NomiChirps/tplp2/tplp/hx8357/lvgl_driver.h

#ifndef TPLP_HX8357_LVGL_DRIVER_H_
#define TPLP_HX8357_LVGL_DRIVER_H_

#include "lvgl/lvgl.h"
#include "tplp/hx8357/hx8357.h"

namespace tplp {

// This driver makes use of the 0th task notification index on the
// lv_timer_handler task.
lv_disp_t* RegisterDisplayDriver_HX8357(int priority, int stack_depth,
                                        HX8357* display,
                                        TaskHandle_t lv_timer_task);

}  // namespace tplp

#endif  // TPLP_HX8357_LVGL_DRIVER_H_
