NomiChirps/tplp2/tplp/tsc2007/tsc2007_lvgl_driver.h

#ifndef TPLP_TSC2007_TSC2007_LVGL_DRIVER_H_
#define TPLP_TSC2007_TSC2007_LVGL_DRIVER_H_

#include "lvgl/lvgl.h"
#include "tplp/tsc2007/tsc2007.h"

namespace tplp {

lv_indev_t* RegisterInputDevice_TSC2007(TSC2007* touchscreen);

}  // namespace tplp

#endif  // TPLP_TSC2007_TSC2007_LVGL_DRIVER_H_
