NomiChirps/tplp2/absl/strings/charconv.cc

// Copyright 2018 The Abseil Authors.
//
// Licensed under the Apache License, Version 2.0 (the "License");
// you may not use this file except in compliance with the License.
// You may obtain a copy of the License at
//
//      https://www.apache.org/licenses/LICENSE-2.0
//
// Unless required by applicable law or agreed to in writing, software
// distributed under the License is distributed on an "AS IS" BASIS,
// WITHOUT WARRANTIES OR CONDITIONS OF ANY KIND, either express or implied.
// See the License for the specific language governing permissions and
// limitations under the License.

#include "absl/strings/charconv.h"

#include <algorithm>
#include <cassert>
#include <cmath>
#include <cstring>
#include <limits>

#include "absl/base/casts.h"
#include "absl/numeric/bits.h"
#include "absl/numeric/int128.h"
#include "absl/strings/internal/charconv_bigint.h"
#include "absl/strings/internal/charconv_parse.h"

// The macro ABSL_BIT_PACK_FLOATS is defined on x86-64, where IEEE floating
// point numbers have the same endianness in memory as a bitfield struct
// containing the corresponding parts.
//
// When set, we replace calls to ldexp() with manual bit packing, which is
// faster and is unaffected by floating point environment.
#ifdef ABSL_BIT_PACK_FLOATS
#error ABSL_BIT_PACK_FLOATS cannot be directly set
#elif defined(__x86_64__) || defined(_M_X64)
#define ABSL_BIT_PACK_FLOATS 1
#endif

// A note about subnormals:
//
// The code below talks about "normals" and "subnormals".  A normal IEEE float
// has a fixed-width mantissa and power of two exponent.  For example, a normal
// `double` has a 53-bit mantissa.  Because the high bit is always 1, it is not
// stored in the representation.  The implicit bit buys an extra bit of
// resolution in the datatype.
//
// The downside of this scheme is that there is a large gap between DBL_MIN and
// zero.  (Large, at least, relative to the different between DBL_MIN and the
// next representable number).  This gap is softened by the "subnormal" numbers,
// which have the same power-of-two exponent as DBL_MIN, but no implicit 53rd
// bit.  An all-bits-zero exponent in the encoding represents subnormals.  (Zero
// is represented as a subnormal with an all-bits-zero mantissa.)
//
// The code below, in calculations, represents the mantissa as a uint64_t.  The
// end result normally has the 53rd bit set.  It represents subnormals by using
// narrower mantissas.

namespace absl {
ABSL_NAMESPACE_BEGIN
namespace {

template <typename FloatType>
struct FloatTraits;

template <>
struct FloatTraits<double> {
  using mantissa_t = uint64_t;

  // The number of mantissa bits in the given float type.  This includes the
  // implied high bit.
  static constexpr int kTargetMantissaBits = 53;

  // The largest supported IEEE exponent, in our integral mantissa
  // representation.
  //
  // If `m` is the largest possible int kTargetMantissaBits bits wide, then
  // m * 2**kMaxExponent is exactly equal to DBL_MAX.
  static constexpr int kMaxExponent = 971;

  // The smallest supported IEEE normal exponent, in our integral mantissa
  // representation.
  //
  // If `m` is the smallest possible int kTargetMantissaBits bits wide, then
  // m * 2**kMinNormalExponent is exactly equal to DBL_MIN.
  static constexpr int kMinNormalExponent = -1074;

  static double MakeNan(const char* tagp) {
    // Support nan no matter which namespace it's in.  Some platforms
    // incorrectly don't put it in namespace std.
    using namespace std;  // NOLINT
    return nan(tagp);
  }

  // Builds a nonzero floating point number out of the provided parts.
  //
  // This is intended to do the same operation as ldexp(mantissa, exponent),
  // but using purely integer math, to avoid -ffastmath and floating
  // point environment issues.  Using type punning is also faster. We fall back
  // to ldexp on a per-platform basis for portability.
  //
  // `exponent` must be between kMinNormalExponent and kMaxExponent.
  //
  // `mantissa` must either be exactly kTargetMantissaBits wide, in which case
  // a normal value is made, or it must be less narrow than that, in which case
  // `exponent` must be exactly kMinNormalExponent, and a subnormal value is
  // made.
  static double Make(mantissa_t mantissa, int exponent, bool sign) {
#ifndef ABSL_BIT_PACK_FLOATS
    // Support ldexp no matter which namespace it's in.  Some platforms
    // incorrectly don't put it in namespace std.
    using namespace std;  // NOLINT
    return sign ? -ldexp(mantissa, exponent) : ldexp(mantissa, exponent);
#else
    constexpr uint64_t kMantissaMask =
        (uint64_t{1} << (kTargetMantissaBits - 1)) - 1;
    uint64_t dbl = static_cast<uint64_t>(sign) << 63;
    if (mantissa > kMantissaMask) {
      // Normal value.
      // Adjust by 1023 for the exponent representation bias, and an additional
      // 52 due to the implied decimal point in the IEEE mantissa
      // representation.
      dbl += static_cast<uint64_t>(exponent + 1023 + kTargetMantissaBits - 1)
             << 52;
      mantissa &= kMantissaMask;
    } else {
      // subnormal value
      assert(exponent == kMinNormalExponent);
    }
    dbl += mantissa;
    return absl::bit_cast<double>(dbl);
#endif  // ABSL_BIT_PACK_FLOATS
  }
};

// Specialization of floating point traits for the `float` type.  See the
// FloatTraits<double> specialization above for meaning of each of the following
// members and methods.
template <>
struct FloatTraits<float> {
  using mantissa_t = uint32_t;

  static constexpr int kTargetMantissaBits = 24;
  static constexpr int kMaxExponent = 104;
  static constexpr int kMinNormalExponent = -149;

  static float MakeNan(const char* tagp) {
    // Support nanf no matter which namespace it's in.  Some platforms
    // incorrectly don't put it in namespace std.
    using namespace std;  // NOLINT
    return nanf(tagp);
  }

  static float Make(mantissa_t mantissa, int exponent, bool sign) {
#ifndef ABSL_BIT_PACK_FLOATS
    // Support ldexpf no matter which namespace it's in.  Some platforms
    // incorrectly don't put it in namespace std.
    using namespace std;  // NOLINT
    return sign ? -ldexpf(mantissa, exponent) : ldexpf(mantissa, exponent);
#else
    constexpr uint32_t kMantissaMask =
        (uint32_t{1} << (kTargetMantissaBits - 1)) - 1;
    uint32_t flt = static_cast<uint32_t>(sign) << 31;
    if (mantissa > kMantissaMask) {
      // Normal value.
      // Adjust by 127 for the exponent representation bias, and an additional
      // 23 due to the implied decimal point in the IEEE mantissa represenation.
      flt += static_cast<uint32_t>(exponent + 127 + kTargetMantissaBits - 1)
             << 23;
      mantissa &= kMantissaMask;
    } else {
      // subnormal value
      assert(exponent == kMinNormalExponent);
    }
    flt += mantissa;
    return absl::bit_cast<float>(flt);
#endif  // ABSL_BIT_PACK_FLOATS
  }
};

// Decimal-to-binary conversions require coercing powers of 10 into a mantissa
// and a power of 2.  The two helper functions Power10Mantissa(n) and
// Power10Exponent(n) perform this task.  Together, these represent a hand-
// rolled floating point value which is equal to or just less than 10**n.
//
// The return values satisfy two range guarantees:
//
//   Power10Mantissa(n) * 2**Power10Exponent(n) <= 10**n
//     < (Power10Mantissa(n) + 1) * 2**Power10Exponent(n)
//
//   2**63 <= Power10Mantissa(n) < 2**64.
//
// Lookups into the power-of-10 table must first check the Power10Overflow() and
// Power10Underflow() functions, to avoid out-of-bounds table access.
//
// Indexes into these tables are biased by -kPower10TableMin, and the table has
// values in the range [kPower10TableMin, kPower10TableMax].
extern const uint64_t kPower10MantissaHighTable[];  // High 64 of 128 bits.
extern const uint64_t kPower10MantissaLowTable[];   // Low  64 of 128 bits.
extern const int16_t kPower10ExponentTable[];

// The smallest (inclusive) allowed value for use with the Power10Mantissa()
// and Power10Exponent() functions below.  (If a smaller exponent is needed in
// calculations, the end result is guaranteed to underflow.)
constexpr int kPower10TableMin = -342;

// The largest (inclusive) allowed value for use with the Power10Mantissa() and
// Power10Exponent() functions below.  (If a smaller exponent is needed in
// calculations, the end result is guaranteed to overflow.)
constexpr int kPower10TableMax = 308;

uint64_t Power10Mantissa(int n) {
  return kPower10MantissaHighTable[n - kPower10TableMin];
}

int Power10Exponent(int n) {
  return kPower10ExponentTable[n - kPower10TableMin];
}

// Returns true if n is large enough that 10**n always results in an IEEE
// overflow.
bool Power10Overflow(int n) { return n > kPower10TableMax; }

// Returns true if n is small enough that 10**n times a ParsedFloat mantissa
// always results in an IEEE underflow.
bool Power10Underflow(int n) { return n < kPower10TableMin; }

// Returns true if Power10Mantissa(n) * 2**Power10Exponent(n) is exactly equal
// to 10**n numerically.  Put another way, this returns true if there is no
// truncation error in Power10Mantissa(n).
bool Power10Exact(int n) { return n >= 0 && n <= 27; }

// Sentinel exponent values for representing numbers too large or too close to
// zero to represent in a double.
constexpr int kOverflow = 99999;
constexpr int kUnderflow = -99999;

// Struct representing the calculated conversion result of a positive (nonzero)
// floating point number.
//
// The calculated number is mantissa * 2**exponent (mantissa is treated as an
// integer.)  `mantissa` is chosen to be the correct width for the IEEE float
// representation being calculated.  (`mantissa` will always have the same bit
// width for normal values, and narrower bit widths for subnormals.)
//
// If the result of conversion was an underflow or overflow, exponent is set
// to kUnderflow or kOverflow.
struct CalculatedFloat {
  uint64_t mantissa = 0;
  int exponent = 0;
};

// Returns the bit width of the given uint128.  (Equivalently, returns 128
// minus the number of leading zero bits.)
int BitWidth(uint128 value) {
  if (Uint128High64(value) == 0) {
    return bit_width(Uint128Low64(value));
  }
  return 128 - countl_zero(Uint128High64(value));
}

// Calculates how far to the right a mantissa needs to be shifted to create a
// properly adjusted mantissa for an IEEE floating point number.
//
// `mantissa_width` is the bit width of the mantissa to be shifted, and
// `binary_exponent` is the exponent of the number before the shift.
//
// This accounts for subnormal values, and will return a larger-than-normal
// shift if binary_exponent would otherwise be too low.
template <typename FloatType>
int NormalizedShiftSize(int mantissa_width, int binary_exponent) {
  const int normal_shift =
      mantissa_width - FloatTraits<FloatType>::kTargetMantissaBits;
  const int minimum_shift =
      FloatTraits<FloatType>::kMinNormalExponent - binary_exponent;
  return std::max(normal_shift, minimum_shift);
}

// Right shifts a uint128 so that it has the requested bit width.  (The
// resulting value will have 128 - bit_width leading zeroes.)  The initial
// `value` must be wider than the requested bit width.
//
// Returns the number of bits shifted.
int TruncateToBitWidth(int bit_width, uint128* value) {
  const int current_bit_width = BitWidth(*value);
  const int shift = current_bit_width - bit_width;
  *value >>= shift;
  return shift;
}

// Checks if the given ParsedFloat represents one of the edge cases that are
// not dependent on number base: zero, infinity, or NaN.  If so, sets *value
// the appropriate double, and returns true.
template <typename FloatType>
bool HandleEdgeCase(const strings_internal::ParsedFloat& input, bool negative,
                    FloatType* value) {
  if (input.type == strings_internal::FloatType::kNan) {
    // A bug in both clang and gcc would cause the compiler to optimize away the
    // buffer we are building below.  Declaring the buffer volatile avoids the
    // issue, and has no measurable performance impact in microbenchmarks.
    //
    // https://bugs.llvm.org/show_bug.cgi?id=37778
    // https://gcc.gnu.org/bugzilla/show_bug.cgi?id=86113
    constexpr ptrdiff_t kNanBufferSize = 128;
    volatile char n_char_sequence[kNanBufferSize];
    if (input.subrange_begin == nullptr) {
      n_char_sequence[0] = '\0';
    } else {
      ptrdiff_t nan_size = input.subrange_end - input.subrange_begin;
      nan_size = std::min(nan_size, kNanBufferSize - 1);
      std::copy_n(input.subrange_begin, nan_size, n_char_sequence);
      n_char_sequence[nan_size] = '\0';
    }
    char* nan_argument = const_cast<char*>(n_char_sequence);
    *value = negative ? -FloatTraits<FloatType>::MakeNan(nan_argument)
                      : FloatTraits<FloatType>::MakeNan(nan_argument);
    return true;
  }
  if (input.type == strings_internal::FloatType::kInfinity) {
    *value = negative ? -std::numeric_limits<FloatType>::infinity()
                      : std::numeric_limits<FloatType>::infinity();
    return true;
  }
  if (input.mantissa == 0) {
    *value = negative ? -0.0 : 0.0;
    return true;
  }
  return false;
}

// Given a CalculatedFloat result of a from_chars conversion, generate the
// correct output values.
//
// CalculatedFloat can represent an underflow or overflow, in which case the
// error code in *result is set.  Otherwise, the calculated floating point
// number is stored in *value.
template <typename FloatType>
void EncodeResult(const CalculatedFloat& calculated, bool negative,
                  absl::from_chars_result* result, FloatType* value) {
  if (calculated.exponent == kOverflow) {
    result->ec = std::errc::result_out_of_range;
    *value = negative ? -std::numeric_limits<FloatType>::max()
                      : std::numeric_limits<FloatType>::max();
    return;
  } else if (calculated.mantissa == 0 || calculated.exponent == kUnderflow) {
    result->ec = std::errc::result_out_of_range;
    *value = negative ? -0.0 : 0.0;
    return;
  }
  *value = FloatTraits<FloatType>::Make(
      static_cast<typename FloatTraits<FloatType>::mantissa_t>(
          calculated.mantissa),
      calculated.exponent, negative);
}

// Returns the given uint128 shifted to the right by `shift` bits, and rounds
// the remaining bits using round_to_nearest logic.  The value is returned as a
// uint64_t, since this is the type used by this library for storing calculated
// floating point mantissas.
//
// It is expected that the width of the input value shifted by `shift` will
// be the correct bit-width for the target mantissa, which is strictly narrower
// than a uint64_t.
//
// If `input_exact` is false, then a nonzero error epsilon is assumed.  For
// rounding purposes, the true value being rounded is strictly greater than the
// input value.  The error may represent a single lost carry bit.
//
// When input_exact, shifted bits of the form 1000000... represent a tie, which
// is broken by rounding to even -- the rounding direction is chosen so the low
// bit of the returned value is 0.
//
// When !input_exact, shifted bits of the form 10000000... represent a value
// strictly greater than one half (due to the error epsilon), and so ties are
// always broken by rounding up.
//
// When !input_exact, shifted bits of the form 01111111... are uncertain;
// the true value may or may not be greater than 10000000..., due to the
// possible lost carry bit.  The correct rounding direction is unknown.  In this
// case, the result is rounded down, and `output_exact` is set to false.
//
// Zero and negative values of `shift` are accepted, in which case the word is
// shifted left, as necessary.
uint64_t ShiftRightAndRound(uint128 value, int shift, bool input_exact,
                            bool* output_exact) {
  if (shift <= 0) {
    *output_exact = input_exact;
    return static_cast<uint64_t>(value << -shift);
  }
  if (shift >= 128) {
    // Exponent is so small that we are shifting away all significant bits.
    // Answer will not be representable, even as a subnormal, so return a zero
    // mantissa (which represents underflow).
    *output_exact = true;
    return 0;
  }

  *output_exact = true;
  const uint128 shift_mask = (uint128(1) << shift) - 1;
  const uint128 halfway_point = uint128(1) << (shift - 1);

  const uint128 shifted_bits = value & shift_mask;
  value >>= shift;
  if (shifted_bits > halfway_point) {
    // Shifted bits greater than 10000... require rounding up.
    return static_cast<uint64_t>(value + 1);
  }
  if (shifted_bits == halfway_point) {
    // In exact mode, shifted bits of 10000... mean we're exactly halfway
    // between two numbers, and we must round to even.  So only round up if
    // the low bit of `value` is set.
    //
    // In inexact mode, the nonzero error means the actual value is greater
    // than the halfway point and we must alway round up.
    if ((value & 1) == 1 || !input_exact) {
      ++value;
    }
    return static_cast<uint64_t>(value);
  }
  if (!input_exact && shifted_bits == halfway_point - 1) {
    // Rounding direction is unclear, due to error.
    *output_exact = false;
  }
  // Otherwise, round down.
  return static_cast<uint64_t>(value);
}

// Checks if a floating point guess needs to be rounded up, using high precision
// math.
//
// `guess_mantissa` and `guess_exponent` represent a candidate guess for the
// number represented by `parsed_decimal`.
//
// The exact number represented by `parsed_decimal` must lie between the two
// numbers:
//   A = `guess_mantissa * 2**guess_exponent`
//   B = `(guess_mantissa + 1) * 2**guess_exponent`
//
// This function returns false if `A` is the better guess, and true if `B` is
// the better guess, with rounding ties broken by rounding to even.
bool MustRoundUp(uint64_t guess_mantissa, int guess_exponent,
                 const strings_internal::ParsedFloat& parsed_decimal) {
  // 768 is the number of digits needed in the worst case.  We could determine a
  // better limit dynamically based on the value of parsed_decimal.exponent.
  // This would optimize pathological input cases only.  (Sane inputs won't have
  // hundreds of digits of mantissa.)
  absl::strings_internal::BigUnsigned<84> exact_mantissa;
  int exact_exponent = exact_mantissa.ReadFloatMantissa(parsed_decimal, 768);

  // Adjust the `guess` arguments to be halfway between A and B.
  guess_mantissa = guess_mantissa * 2 + 1;
  guess_exponent -= 1;

  // In our comparison:
  // lhs = exact = exact_mantissa * 10**exact_exponent
  //             = exact_mantissa * 5**exact_exponent * 2**exact_exponent
  // rhs = guess = guess_mantissa * 2**guess_exponent
  //
  // Because we are doing integer math, we can't directly deal with negative
  // exponents.  We instead move these to the other side of the inequality.
  absl::strings_internal::BigUnsigned<84>& lhs = exact_mantissa;
  int comparison;
  if (exact_exponent >= 0) {
    lhs.MultiplyByFiveToTheNth(exact_exponent);
    absl::strings_internal::BigUnsigned<84> rhs(guess_mantissa);
    // There are powers of 2 on both sides of the inequality; reduce this to
    // a single bit-shift.
    if (exact_exponent > guess_exponent) {
      lhs.ShiftLeft(exact_exponent - guess_exponent);
    } else {
      rhs.ShiftLeft(guess_exponent - exact_exponent);
    }
    comparison = Compare(lhs, rhs);
  } else {
    // Move the power of 5 to the other side of the equation, giving us:
    // lhs = exact_mantissa * 2**exact_exponent
    // rhs = guess_mantissa * 5**(-exact_exponent) * 2**guess_exponent
    absl::strings_internal::BigUnsigned<84> rhs =
        absl::strings_internal::BigUnsigned<84>::FiveToTheNth(-exact_exponent);
    rhs.MultiplyBy(guess_mantissa);
    if (exact_exponent > guess_exponent) {
      lhs.ShiftLeft(exact_exponent - guess_exponent);
    } else {
      rhs.ShiftLeft(guess_exponent - exact_exponent);
    }
    comparison = Compare(lhs, rhs);
  }
  if (comparison < 0) {
    return false;
  } else if (comparison > 0) {
    return true;
  } else {
    // When lhs == rhs, the decimal input is exactly between A and B.
    // Round towards even -- round up only if the low bit of the initial
    // `guess_mantissa` was a 1.  We shifted guess_mantissa left 1 bit at
    // the beginning of this function, so test the 2nd bit here.
    return (guess_mantissa & 2) == 2;
  }
}

// Constructs a CalculatedFloat from a given mantissa and exponent, but
// with the following normalizations applied:
//
// If rounding has caused mantissa to increase just past the allowed bit
// width, shift and adjust exponent.
//
// If exponent is too high, sets kOverflow.
//
// If mantissa is zero (representing a non-zero value not representable, even
// as a subnormal), sets kUnderflow.
template <typename FloatType>
CalculatedFloat CalculatedFloatFromRawValues(uint64_t mantissa, int exponent) {
  CalculatedFloat result;
  if (mantissa == uint64_t{1} << FloatTraits<FloatType>::kTargetMantissaBits) {
    mantissa >>= 1;
    exponent += 1;
  }
  if (exponent > FloatTraits<FloatType>::kMaxExponent) {
    result.exponent = kOverflow;
  } else if (mantissa == 0) {
    result.exponent = kUnderflow;
  } else {
    result.exponent = exponent;
    result.mantissa = mantissa;
  }
  return result;
}

template <typename FloatType>
CalculatedFloat CalculateFromParsedHexadecimal(
    const strings_internal::ParsedFloat& parsed_hex) {
  uint64_t mantissa = parsed_hex.mantissa;
  int exponent = parsed_hex.exponent;
  int mantissa_width = bit_width(mantissa);
  const int shift = NormalizedShiftSize<FloatType>(mantissa_width, exponent);
  bool result_exact;
  exponent += shift;
  mantissa = ShiftRightAndRound(mantissa, shift,
                                /* input exact= */ true, &result_exact);
  // ParseFloat handles rounding in the hexadecimal case, so we don't have to
  // check `result_exact` here.
  return CalculatedFloatFromRawValues<FloatType>(mantissa, exponent);
}

template <typename FloatType>
CalculatedFloat CalculateFromParsedDecimal(
    const strings_internal::ParsedFloat& parsed_decimal) {
  CalculatedFloat result;

  // Large or small enough decimal exponents will always result in overflow
  // or underflow.
  if (Power10Underflow(parsed_decimal.exponent)) {
    result.exponent = kUnderflow;
    return result;
  } else if (Power10Overflow(parsed_decimal.exponent)) {
    result.exponent = kOverflow;
    return result;
  }

  // Otherwise convert our power of 10 into a power of 2 times an integer
  // mantissa, and multiply this by our parsed decimal mantissa.
  uint128 wide_binary_mantissa = parsed_decimal.mantissa;
  wide_binary_mantissa *= Power10Mantissa(parsed_decimal.exponent);
  int binary_exponent = Power10Exponent(parsed_decimal.exponent);

  // Discard bits that are inaccurate due to truncation error.  The magic
  // `mantissa_width` constants below are justified in
  // https://abseil.io/about/design/charconv. They represent the number of bits
  // in `wide_binary_mantissa` that are guaranteed to be unaffected by error
  // propagation.
  bool mantissa_exact;
  int mantissa_width;
  if (parsed_decimal.subrange_begin) {
    // Truncated mantissa
    mantissa_width = 58;
    mantissa_exact = false;
    binary_exponent +=
        TruncateToBitWidth(mantissa_width, &wide_binary_mantissa);
  } else if (!Power10Exact(parsed_decimal.exponent)) {
    // Exact mantissa, truncated power of ten
    mantissa_width = 63;
    mantissa_exact = false;
    binary_exponent +=
        TruncateToBitWidth(mantissa_width, &wide_binary_mantissa);
  } else {
    // Product is exact
    mantissa_width = BitWidth(wide_binary_mantissa);
    mantissa_exact = true;
  }

  // Shift into an FloatType-sized mantissa, and round to nearest.
  const int shift =
      NormalizedShiftSize<FloatType>(mantissa_width, binary_exponent);
  bool result_exact;
  binary_exponent += shift;
  uint64_t binary_mantissa = ShiftRightAndRound(wide_binary_mantissa, shift,
                                                mantissa_exact, &result_exact);
  if (!result_exact) {
    // We could not determine the rounding direction using int128 math.  Use
    // full resolution math instead.
    if (MustRoundUp(binary_mantissa, binary_exponent, parsed_decimal)) {
      binary_mantissa += 1;
    }
  }

  return CalculatedFloatFromRawValues<FloatType>(binary_mantissa,
                                                 binary_exponent);
}

// As discussed in https://nigeltao.github.io/blog/2020/eisel-lemire.html the
// primary goal of the Eisel-Lemire algorithm is speed, for 99+% of the cases,
// not 100% coverage. As long as Eisel-Lemire doesn’t claim false positives,
// the combined approach (falling back to an alternative implementation when
// this function returns false) is both fast and correct.
template <typename FloatType>
bool EiselLemire(const strings_internal::ParsedFloat& input, bool negative,
                 FloatType* value) {
  // For now, implement Eisel-Lemire only for double, not float.
  if (FloatTraits<FloatType>::kTargetMantissaBits != 53) {
    return false;
  }

  uint64_t man = input.mantissa;
  int exp10 = input.exponent;
  if (Power10Underflow(exp10) || Power10Overflow(exp10)) {
    return false;
  }

  // The terse (+) comments in this function body refer to sections of the
  // https://nigeltao.github.io/blog/2020/eisel-lemire.html blog post.
  //
  // See also "Number Parsing at a Gigabyte per Second, Software: Practice and
  // Experience 51 (8), 2021" (https://arxiv.org/abs/2101.11408) for detail.

  // (+) Normalization.
  int clz = countl_zero(man);
  man <<= static_cast<unsigned int>(clz);
  static constexpr int exp2_bias = 1023;
  // The 217706 etc magic numbers encode the kPower10ExponentTable as a formula
  // instead of a table. Their equivalence is confirmed by
  // https://github.com/google/wuffs/blob/315b2e52625ebd7b02d8fac13e3cd85ea374fb80/script/print-mpb-powers-of-10.go
  uint64_t ret_exp2 =
      static_cast<uint64_t>((217706 * exp10 >> 16) + 64 + exp2_bias - clz);

  // (+) Multiplication.
  uint128 x =
      static_cast<uint128>(man) *
      static_cast<uint128>(kPower10MantissaHighTable[exp10 - kPower10TableMin]);

  // (+) Wider Approximation.
  if (((Uint128High64(x) & 0x1FF) == 0x1FF) &&
      (man > (std::numeric_limits<uint64_t>::max() - Uint128Low64(x)))) {
    uint128 y = static_cast<uint128>(man) *
                static_cast<uint128>(
                    kPower10MantissaLowTable[exp10 - kPower10TableMin]);
    x += Uint128High64(y);
    // For example, parsing "4503599627370497.5" will take the if-true
    // branch here, since:
    //  - x   = 0x8000000000000BFF_FFFFFFFFFFFFFFFF
    //  - y   = 0x8000000000000BFF_7FFFFFFFFFFFF400
    //  - man = 0xA000000000000F00
    if (((Uint128High64(x) & 0x1FF) == 0x1FF) && ((Uint128Low64(x) + 1) == 0) &&
        (man > (std::numeric_limits<uint64_t>::max() - Uint128Low64(y)))) {
      return false;
    }
  }

  // (+) Shifting to 54 Bits.
  uint64_t msb = Uint128High64(x) >> 63;
  uint64_t ret_man = Uint128High64(x) >> (msb + 9);
  ret_exp2 -= 1 ^ msb;

  // (+) Half-way Ambiguity.
  //
  // For example, parsing "1e+23" will take the if-true branch here, since:
  //  - x       = 0x54B40B1F852BDA00_0000000000000000
  //  - ret_man = 0x002A5A058FC295ED
  if ((Uint128Low64(x) == 0) && ((Uint128High64(x) & 0x1FF) == 0) &&
      ((ret_man & 3) == 1)) {
    return false;
  }

  // (+) From 54 to 53 Bits.
  ret_man += ret_man & 1;  // Line From54a.
  ret_man >>= 1;           // Line From54b.
  // Incrementing ret_man (at line From54a) may have overflowed 54 bits (53
  // bits after the right shift by 1 at line From54b), so adjust for that.
  //
  // For example, parsing "9223372036854775807" will take the if-true branch
  // here, since ret_man = 0x0020000000000000 = (1 << 53).
  if ((ret_man >> 53) > 0) {
    ret_exp2 += 1;
    // Conceptually, we need a "ret_man >>= 1" in this if-block to balance
    // incrementing ret_exp2 in the line immediately above. However, we only
    // get here when line From54a overflowed (after adding a 1), so ret_man
    // here is (1 << 53). Its low 53 bits are therefore all zeroes. The only
    // remaining use of ret_man is to mask it with ((1 << 52) - 1), so only its
    // low 52 bits matter. A "ret_man >>= 1" would have no effect in practice.
    //
    // We omit the "ret_man >>= 1", even if it is cheap (and this if-branch is
    // rarely taken) and technically 'more correct', so that mutation tests
    // that would otherwise modify or omit that "ret_man >>= 1" don't complain
    // that such code mutations have no observable effect.
  }

  // ret_exp2 is a uint64_t. Zero or underflow means that we're in subnormal
  // space. 0x7FF or above means that we're in Inf/NaN space.
  //
  // The if block is equivalent to (but has fewer branches than):
  //   if ((ret_exp2 <= 0) || (ret_exp2 >= 0x7FF)) { etc }
  //
  // For example, parsing "4.9406564584124654e-324" will take the if-true
  // branch here, since ret_exp2 = -51.
  if ((ret_exp2 - 1) >= (0x7FF - 1)) {
    return false;
  }

#ifndef ABSL_BIT_PACK_FLOATS
  *value = FloatTraits<FloatType>::Make(
      (ret_man & 0x000FFFFFFFFFFFFFu) | 0x0010000000000000u,
      ret_exp2 - 1023 - 52, negative);
#else
  uint64_t ret_bits = (ret_exp2 << 52) | (ret_man & 0x000FFFFFFFFFFFFFu);
  if (negative) {
    ret_bits |= 0x8000000000000000u;
  }
  *value = absl::bit_cast<double>(ret_bits);
#endif  // ABSL_BIT_PACK_FLOATS
  return true;
}

template <typename FloatType>
from_chars_result FromCharsImpl(const char* first, const char* last,
                                FloatType& value, chars_format fmt_flags) {
  from_chars_result result;
  result.ptr = first;  // overwritten on successful parse
  result.ec = std::errc();

  bool negative = false;
  if (first != last && *first == '-') {
    ++first;
    negative = true;
  }
  // If the `hex` flag is *not* set, then we will accept a 0x prefix and try
  // to parse a hexadecimal float.
  if ((fmt_flags & chars_format::hex) == chars_format{} && last - first >= 2 &&
      *first == '0' && (first[1] == 'x' || first[1] == 'X')) {
    const char* hex_first = first + 2;
    strings_internal::ParsedFloat hex_parse =
        strings_internal::ParseFloat<16>(hex_first, last, fmt_flags);
    if (hex_parse.end == nullptr ||
        hex_parse.type != strings_internal::FloatType::kNumber) {
      // Either we failed to parse a hex float after the "0x", or we read
      // "0xinf" or "0xnan" which we don't want to match.
      //
      // However, a string that begins with "0x" also begins with "0", which
      // is normally a valid match for the number zero.  So we want these
      // strings to match zero unless fmt_flags is `scientific`.  (This flag
      // means an exponent is required, which the string "0" does not have.)
      if (fmt_flags == chars_format::scientific) {
        result.ec = std::errc::invalid_argument;
      } else {
        result.ptr = first + 1;
        value = negative ? -0.0 : 0.0;
      }
      return result;
    }
    // We matched a value.
    result.ptr = hex_parse.end;
    if (HandleEdgeCase(hex_parse, negative, &value)) {
      return result;
    }
    CalculatedFloat calculated =
        CalculateFromParsedHexadecimal<FloatType>(hex_parse);
    EncodeResult(calculated, negative, &result, &value);
    return result;
  }
  // Otherwise, we choose the number base based on the flags.
  if ((fmt_flags & chars_format::hex) == chars_format::hex) {
    strings_internal::ParsedFloat hex_parse =
        strings_internal::ParseFloat<16>(first, last, fmt_flags);
    if (hex_parse.end == nullptr) {
      result.ec = std::errc::invalid_argument;
      return result;
    }
    result.ptr = hex_parse.end;
    if (HandleEdgeCase(hex_parse, negative, &value)) {
      return result;
    }
    CalculatedFloat calculated =
        CalculateFromParsedHexadecimal<FloatType>(hex_parse);
    EncodeResult(calculated, negative, &result, &value);
    return result;
  } else {
    strings_internal::ParsedFloat decimal_parse =
        strings_internal::ParseFloat<10>(first, last, fmt_flags);
    if (decimal_parse.end == nullptr) {
      result.ec = std::errc::invalid_argument;
      return result;
    }
    result.ptr = decimal_parse.end;
    if (HandleEdgeCase(decimal_parse, negative, &value)) {
      return result;
    }
    // A nullptr subrange_begin means that the decimal_parse.mantissa is exact
    // (not truncated), a precondition of the Eisel-Lemire algorithm.
    if ((decimal_parse.subrange_begin == nullptr) &&
        EiselLemire<FloatType>(decimal_parse, negative, &value)) {
      return result;
    }
    CalculatedFloat calculated =
        CalculateFromParsedDecimal<FloatType>(decimal_parse);
    EncodeResult(calculated, negative, &result, &value);
    return result;
  }
}
}  // namespace

from_chars_result from_chars(const char* first, const char* last, double& value,
                             chars_format fmt) {
  return FromCharsImpl(first, last, value, fmt);
}

from_chars_result from_chars(const char* first, const char* last, float& value,
                             chars_format fmt) {
  return FromCharsImpl(first, last, value, fmt);
}

namespace {

// Table of powers of 10, from kPower10TableMin to kPower10TableMax.
//
// kPower10MantissaHighTable[i - kPower10TableMin] stores the 64-bit mantissa
// (high bit always on), and kPower10ExponentTable[i - kPower10TableMin] stores
// the power-of-two exponent.  For a given number i, this gives the unique
// mantissa and exponent such that mantissa * 2**exponent <= 10**i < (mantissa
// + 1) * 2**exponent.
//
// kPower10MantissaLowTable extends that 64-bit mantissa to 128 bits.
//
// The tables were generated by
// https://github.com/google/wuffs/blob/315b2e52625ebd7b02d8fac13e3cd85ea374fb80/script/print-mpb-powers-of-10.go
// after re-formatting its output into two arrays of N uint64_t values (instead
// of an N element array of uint64_t pairs).

const uint64_t kPower10MantissaHighTable[] = {
    0xeef453d6923bd65aU, 0x9558b4661b6565f8U, 0xbaaee17fa23ebf76U,
    0xe95a99df8ace6f53U, 0x91d8a02bb6c10594U, 0xb64ec836a47146f9U,
    0xe3e27a444d8d98b7U, 0x8e6d8c6ab0787f72U, 0xb208ef855c969f4fU,
    0xde8b2b66b3bc4723U, 0x8b16fb203055ac76U, 0xaddcb9e83c6b1793U,
    0xd953e8624b85dd78U, 0x87d4713d6f33aa6bU, 0xa9c98d8ccb009506U,
    0xd43bf0effdc0ba48U, 0x84a57695fe98746dU, 0xa5ced43b7e3e9188U,
    0xcf42894a5dce35eaU, 0x818995ce7aa0e1b2U, 0xa1ebfb4219491a1fU,
    0xca66fa129f9b60a6U, 0xfd00b897478238d0U, 0x9e20735e8cb16382U,
    0xc5a890362fddbc62U, 0xf712b443bbd52b7bU, 0x9a6bb0aa55653b2dU,
    0xc1069cd4eabe89f8U, 0xf148440a256e2c76U, 0x96cd2a865764dbcaU,
    0xbc807527ed3e12bcU, 0xeba09271e88d976bU, 0x93445b8731587ea3U,
    0xb8157268fdae9e4cU, 0xe61acf033d1a45dfU, 0x8fd0c16206306babU,
    0xb3c4f1ba87bc8696U, 0xe0b62e2929aba83cU, 0x8c71dcd9ba0b4925U,
    0xaf8e5410288e1b6fU, 0xdb71e91432b1a24aU, 0x892731ac9faf056eU,
    0xab70fe17c79ac6caU, 0xd64d3d9db981787dU, 0x85f0468293f0eb4eU,
    0xa76c582338ed2621U, 0xd1476e2c07286faaU, 0x82cca4db847945caU,
    0xa37fce126597973cU, 0xcc5fc196fefd7d0cU, 0xff77b1fcbebcdc4fU,
    0x9faacf3df73609b1U, 0xc795830d75038c1dU, 0xf97ae3d0d2446f25U,
    0x9becce62836ac577U, 0xc2e801fb244576d5U, 0xf3a20279ed56d48aU,
    0x9845418c345644d6U, 0xbe5691ef416bd60cU, 0xedec366b11c6cb8fU,
    0x94b3a202eb1c3f39U, 0xb9e08a83a5e34f07U, 0xe858ad248f5c22c9U,
    0x91376c36d99995beU, 0xb58547448ffffb2dU, 0xe2e69915b3fff9f9U,
    0x8dd01fad907ffc3bU, 0xb1442798f49ffb4aU, 0xdd95317f31c7fa1dU,
    0x8a7d3eef7f1cfc52U, 0xad1c8eab5ee43b66U, 0xd863b256369d4a40U,
    0x873e4f75e2224e68U, 0xa90de3535aaae202U, 0xd3515c2831559a83U,
    0x8412d9991ed58091U, 0xa5178fff668ae0b6U, 0xce5d73ff402d98e3U,
    0x80fa687f881c7f8eU, 0xa139029f6a239f72U, 0xc987434744ac874eU,
    0xfbe9141915d7a922U, 0x9d71ac8fada6c9b5U, 0xc4ce17b399107c22U,
    0xf6019da07f549b2bU, 0x99c102844f94e0fbU, 0xc0314325637a1939U,
    0xf03d93eebc589f88U, 0x96267c7535b763b5U, 0xbbb01b9283253ca2U,
    0xea9c227723ee8bcbU, 0x92a1958a7675175fU, 0xb749faed14125d36U,
    0xe51c79a85916f484U, 0x8f31cc0937ae58d2U, 0xb2fe3f0b8599ef07U,
    0xdfbdcece67006ac9U, 0x8bd6a141006042bdU, 0xaecc49914078536dU,
    0xda7f5bf590966848U, 0x888f99797a5e012dU, 0xaab37fd7d8f58178U,
    0xd5605fcdcf32e1d6U, 0x855c3be0a17fcd26U, 0xa6b34ad8c9dfc06fU,
    0xd0601d8efc57b08bU, 0x823c12795db6ce57U, 0xa2cb1717b52481edU,
    0xcb7ddcdda26da268U, 0xfe5d54150b090b02U, 0x9efa548d26e5a6e1U,
    0xc6b8e9b0709f109aU, 0xf867241c8cc6d4c0U, 0x9b407691d7fc44f8U,
    0xc21094364dfb5636U, 0xf294b943e17a2bc4U, 0x979cf3ca6cec5b5aU,
    0xbd8430bd08277231U, 0xece53cec4a314ebdU, 0x940f4613ae5ed136U,
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
};

const uint64_t kPower10MantissaLowTable[] = {
    0x113faa2906a13b3fU, 0x4ac7ca59a424c507U, 0x5d79bcf00d2df649U,
    0xf4d82c2c107973dcU, 0x79071b9b8a4be869U, 0x9748e2826cdee284U,
    0xfd1b1b2308169b25U, 0xfe30f0f5e50e20f7U, 0xbdbd2d335e51a935U,
    0xad2c788035e61382U, 0x4c3bcb5021afcc31U, 0xdf4abe242a1bbf3dU,
    0xd71d6dad34a2af0dU, 0x8672648c40e5ad68U, 0x680efdaf511f18c2U,
    0x0212bd1b2566def2U, 0x014bb630f7604b57U, 0x419ea3bd35385e2dU,
    0x52064cac828675b9U, 0x7343efebd1940993U, 0x1014ebe6c5f90bf8U,
    0xd41a26e077774ef6U, 0x8920b098955522b4U, 0x55b46e5f5d5535b0U,
    0xeb2189f734aa831dU, 0xa5e9ec7501d523e4U, 0x47b233c92125366eU,
    0x999ec0bb696e840aU, 0xc00670ea43ca250dU, 0x380406926a5e5728U,
    0xc605083704f5ecf2U, 0xf7864a44c633682eU, 0x7ab3ee6afbe0211dU,
    0x5960ea05bad82964U, 0x6fb92487298e33bdU, 0xa5d3b6d479f8e056U,
    0x8f48a4899877186cU, 0x331acdabfe94de87U, 0x9ff0c08b7f1d0b14U,
    0x07ecf0ae5ee44dd9U, 0xc9e82cd9f69d6150U, 0xbe311c083a225cd2U,
    0x6dbd630a48aaf406U, 0x092cbbccdad5b108U, 0x25bbf56008c58ea5U,
    0xaf2af2b80af6f24eU, 0x1af5af660db4aee1U, 0x50d98d9fc890ed4dU,
    0xe50ff107bab528a0U, 0x1e53ed49a96272c8U, 0x25e8e89c13bb0f7aU,
    0x77b191618c54e9acU, 0xd59df5b9ef6a2417U, 0x4b0573286b44ad1dU,
    0x4ee367f9430aec32U, 0x229c41f793cda73fU, 0x6b43527578c1110fU,
    0x830a13896b78aaa9U, 0x23cc986bc656d553U, 0x2cbfbe86b7ec8aa8U,
    0x7bf7d71432f3d6a9U, 0xdaf5ccd93fb0cc53U, 0xd1b3400f8f9cff68U,
    0x23100809b9c21fa1U, 0xabd40a0c2832a78aU, 0x16c90c8f323f516cU,
    0xae3da7d97f6792e3U, 0x99cd11cfdf41779cU, 0x40405643d711d583U,
    0x482835ea666b2572U, 0xda3243650005eecfU, 0x90bed43e40076a82U,
    0x5a7744a6e804a291U, 0x711515d0a205cb36U, 0x0d5a5b44ca873e03U,
    0xe858790afe9486c2U, 0x626e974dbe39a872U, 0xfb0a3d212dc8128fU,
    0x7ce66634bc9d0b99U, 0x1c1fffc1ebc44e80U, 0xa327ffb266b56220U,
    0x4bf1ff9f0062baa8U, 0x6f773fc3603db4a9U, 0xcb550fb4384d21d3U,
    0x7e2a53a146606a48U, 0x2eda7444cbfc426dU, 0xfa911155fefb5308U,
    0x793555ab7eba27caU, 0x4bc1558b2f3458deU, 0x9eb1aaedfb016f16U,
    0x465e15a979c1cadcU, 0x0bfacd89ec191ec9U, 0xcef980ec671f667bU,
    0x82b7e12780e7401aU, 0xd1b2ecb8b0908810U, 0x861fa7e6dcb4aa15U,
    0x67a791e093e1d49aU, 0xe0c8bb2c5c6d24e0U, 0x58fae9f773886e18U,
    0xaf39a475506a899eU, 0x6d8406c952429603U, 0xc8e5087ba6d33b83U,
    0xfb1e4a9a90880a64U, 0x5cf2eea09a55067fU, 0xf42faa48c0ea481eU,
    0xf13b94daf124da26U, 0x76c53d08d6b70858U, 0x54768c4b0c64ca6eU,
    0xa9942f5dcf7dfd09U, 0xd3f93b35435d7c4cU, 0xc47bc5014a1a6dafU,
    0x359ab6419ca1091bU, 0xc30163d203c94b62U, 0x79e0de63425dcf1dU,
    0x985915fc12f542e4U, 0x3e6f5b7b17b2939dU, 0xa705992ceecf9c42U,
    0x50c6ff782a838353U, 0xa4f8bf5635246428U, 0x871b7795e136be99U,
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
};

const int16_t kPower10ExponentTable[] = {
    -1200, -1196, -1193, -1190, -1186, -1183, -1180, -1176, -1173, -1170, -1166,
    -1163, -1160, -1156, -1153, -1150, -1146, -1143, -1140, -1136, -1133, -1130,
    -1127, -1123, -1120, -1117, -1113, -1110, -1107, -1103, -1100, -1097, -1093,
    -1090, -1087, -1083, -1080, -1077, -1073, -1070, -1067, -1063, -1060, -1057,
    -1053, -1050, -1047, -1043, -1040, -1037, -1034, -1030, -1027, -1024, -1020,
    -1017, -1014, -1010, -1007, -1004, -1000, -997,  -994,  -990,  -987,  -984,
    -980,  -977,  -974,  -970,  -967,  -964,  -960,  -957,  -954,  -950,  -947,
    -944,  -940,  -937,  -934,  -931,  -927,  -924,  -921,  -917,  -914,  -911,
    -907,  -904,  -901,  -897,  -894,  -891,  -887,  -884,  -881,  -877,  -874,
    -871,  -867,  -864,  -861,  -857,  -854,  -851,  -847,  -844,  -841,  -838,
    -834,  -831,  -828,  -824,  -821,  -818,  -814,  -811,  -808,  -804,  -801,
    -798,  -794,  -791,  -788,  -784,  -781,  -778,  -774,  -771,  -768,  -764,
    -761,  -758,  -754,  -751,  -748,  -744,  -741,  -738,  -735,  -731,  -728,
    -725,  -721,  -718,  -715,  -711,  -708,  -705,  -701,  -698,  -695,  -691,
    -688,  -685,  -681,  -678,  -675,  -671,  -668,  -665,  -661,  -658,  -655,
    -651,  -648,  -645,  -642,  -638,  -635,  -632,  -628,  -625,  -622,  -618,
    -615,  -612,  -608,  -605,  -602,  -598,  -595,  -592,  -588,  -585,  -582,
    -578,  -575,  -572,  -568,  -565,  -562,  -558,  -555,  -552,  -549,  -545,
    -542,  -539,  -535,  -532,  -529,  -525,  -522,  -519,  -515,  -512,  -509,
    -505,  -502,  -499,  -495,  -492,  -489,  -485,  -482,  -479,  -475,  -472,
    -469,  -465,  -462,  -459,  -455,  -452,  -449,  -446,  -442,  -439,  -436,
    -432,  -429,  -426,  -422,  -419,  -416,  -412,  -409,  -406,  -402,  -399,
    -396,  -392,  -389,  -386,  -382,  -379,  -376,  -372,  -369,  -366,  -362,
    -359,  -356,  -353,  -349,  -346,  -343,  -339,  -336,  -333,  -329,  -326,
    -323,  -319,  -316,  -313,  -309,  -306,  -303,  -299,  -296,  -293,  -289,
    -286,  -283,  -279,  -276,  -273,  -269,  -266,  -263,  -259,  -256,  -253,
    -250,  -246,  -243,  -240,  -236,  -233,  -230,  -226,  -223,  -220,  -216,
    -213,  -210,  -206,  -203,  -200,  -196,  -193,  -190,  -186,  -183,  -180,
    -176,  -173,  -170,  -166,  -163,  -160,  -157,  -153,  -150,  -147,  -143,
    -140,  -137,  -133,  -130,  -127,  -123,  -120,  -117,  -113,  -110,  -107,
    -103,  -100,  -97,   -93,   -90,   -87,   -83,   -80,   -77,   -73,   -70,
    -67,   -63,   -60,   -57,   -54,   -50,   -47,   -44,   -40,   -37,   -34,
    -30,   -27,   -24,   -20,   -17,   -14,   -10,   -7,    -4,    0,     3,
    6,     10,    13,    16,    20,    23,    26,    30,    33,    36,    39,
    43,    46,    49,    53,    56,    59,    63,    66,    69,    73,    76,
    79,    83,    86,    89,    93,    96,    99,    103,   106,   109,   113,
    116,   119,   123,   126,   129,   132,   136,   139,   142,   146,   149,
    152,   156,   159,   162,   166,   169,   172,   176,   179,   182,   186,
    189,   192,   196,   199,   202,   206,   209,   212,   216,   219,   222,
    226,   229,   232,   235,   239,   242,   245,   249,   252,   255,   259,
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
};

}  // namespace
ABSL_NAMESPACE_END
}  // namespace absl
